William-Dorsch/Open-Source-Train-Controller/train controller parts/automaticBrakeMagnetBase.stl

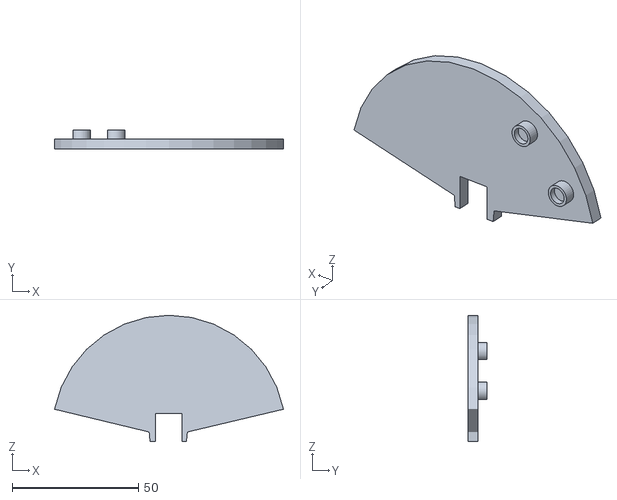
[picture p15: CAD file, 2024-12-01]
train controller parts/automaticBrakeMagnetBase.stl
90.9 x 7.53 x 50.2
