William-Dorsch/Open-Source-Train-Controller/train controller parts/frontWall.stl

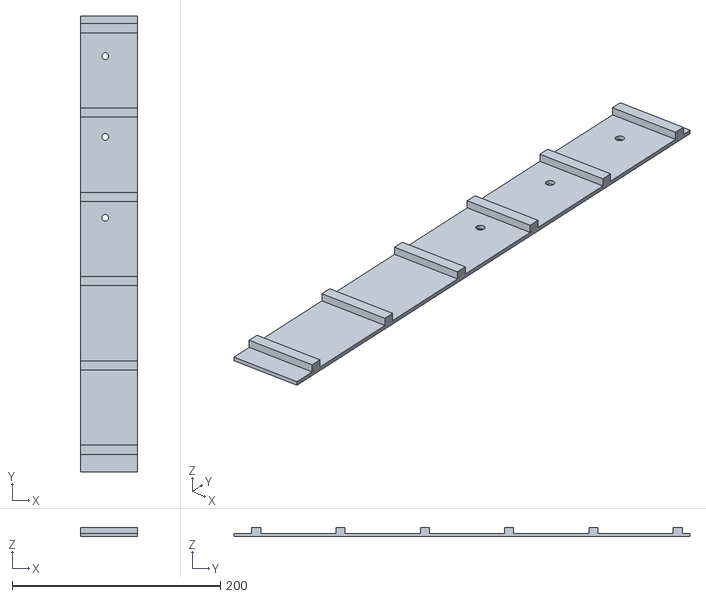
[picture p16: CAD file, 2024-12-01]
train controller parts/frontWall.stl
54.9 x 438.3 x 8.45
