William-Dorsch/Open-Source-Train-Controller/train controller parts/leverWheelBase.stl

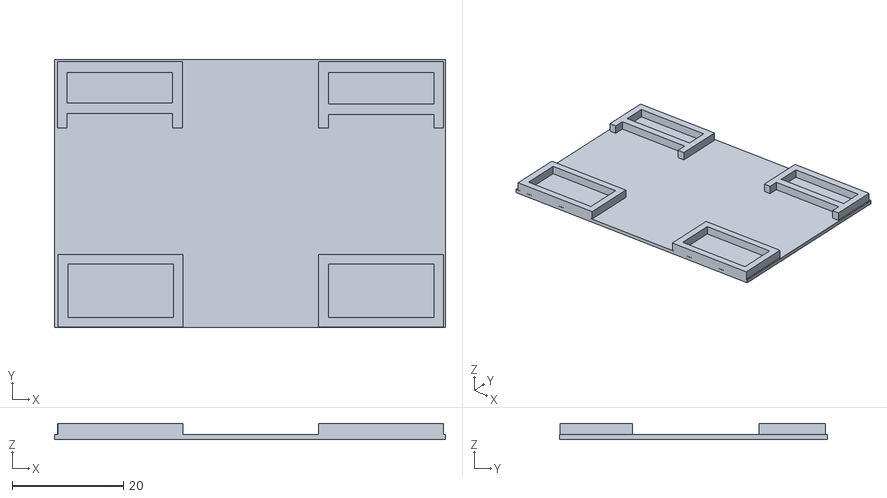
[picture p17: CAD file, 2024-12-01]
train controller parts/leverWheelBase.stl
70.3 x 48.2 x 2.90
