William-Dorsch/Open-Source-Train-Controller/train controller parts/sideWall.stl

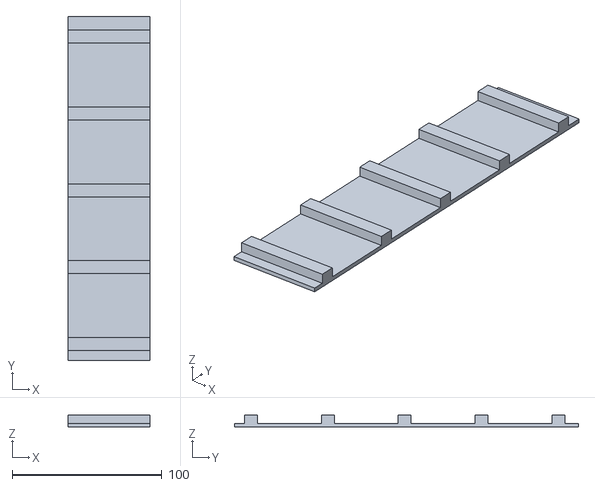
[picture p18: CAD file, 2024-12-01]
train controller parts/sideWall.stl
54.9 x 230.0 x 7.86
