William-Dorsch/Open-Source-Train-Controller/train controller parts/handleBaseRod.stl

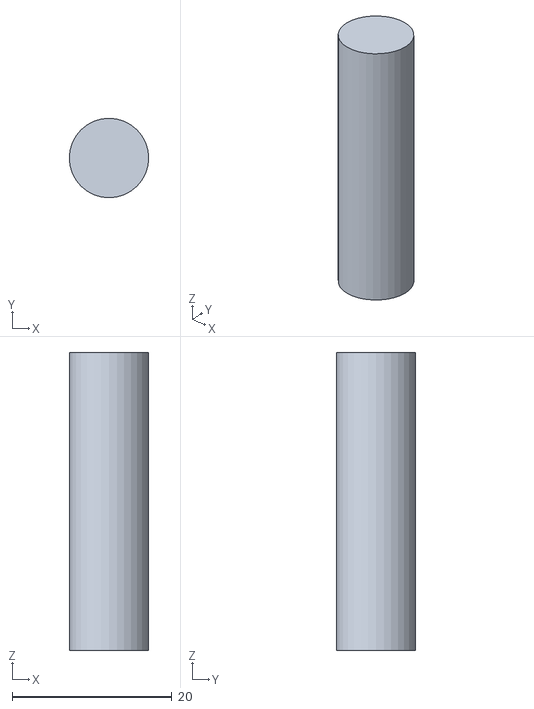
[picture p19: CAD file, 2024-12-01]
train controller parts/handleBaseRod.stl
9.95 x 9.95 x 37.3
