William-Dorsch/Open-Source-Train-Controller/train controller parts/buttonBoardSupports.stl

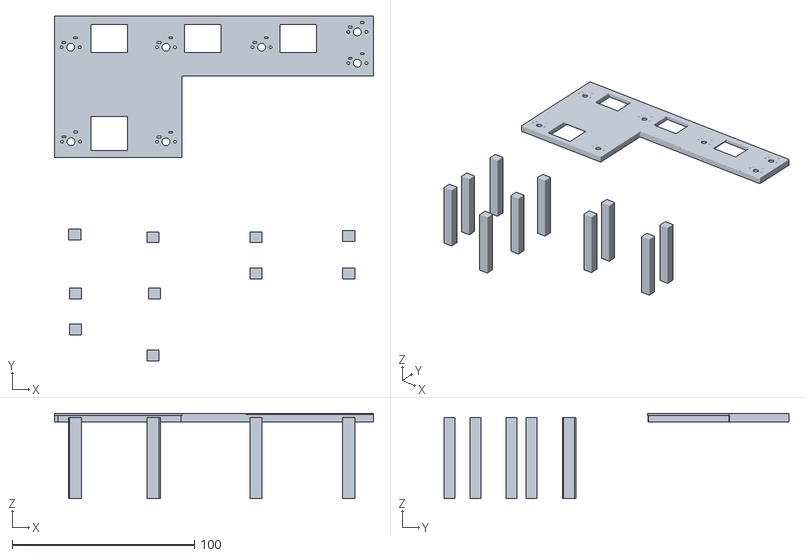
[picture p20: CAD file, 2024-12-01]
train controller parts/buttonBoardSupports.stl
175.0 x 189.2 x 46.6
