William-Dorsch/Open-Source-Train-Controller/train controller parts/lightDial.stl

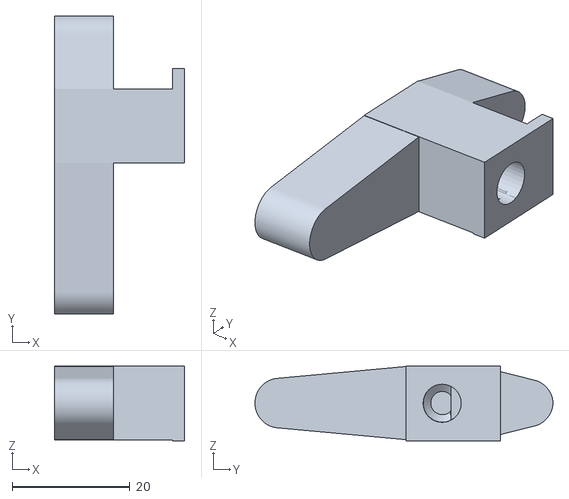
[picture p21: CAD file, 2024-12-01]
train controller parts/lightDial.stl
22.1 x 50.5 x 12.7
