William-Dorsch/Open-Source-Train-Controller/train controller parts/automaticBrakeHandle.stl

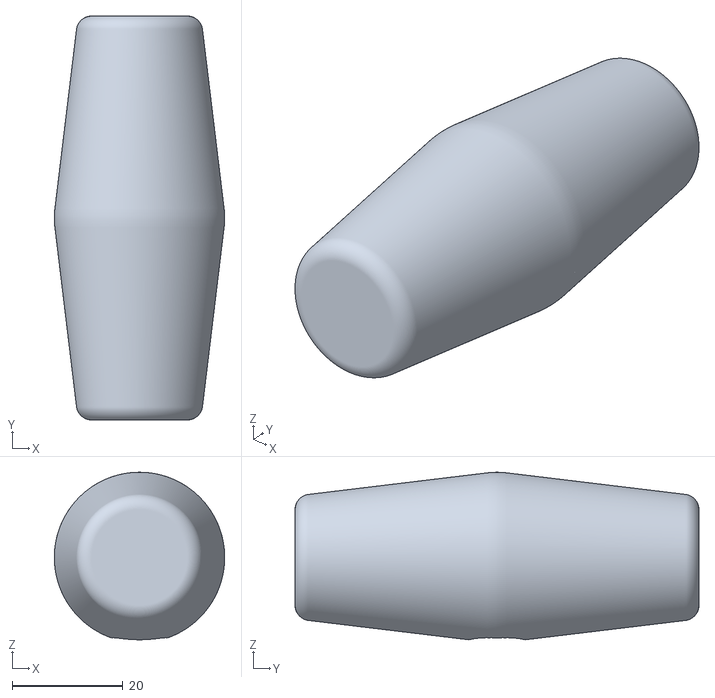
[picture p22: CAD file, 2024-12-01]
train controller parts/automaticBrakeHandle.stl
30.8 x 73.0 x 30.3
