William-Dorsch/Open-Source-Train-Controller/train controller parts/leftLeverCover.stl

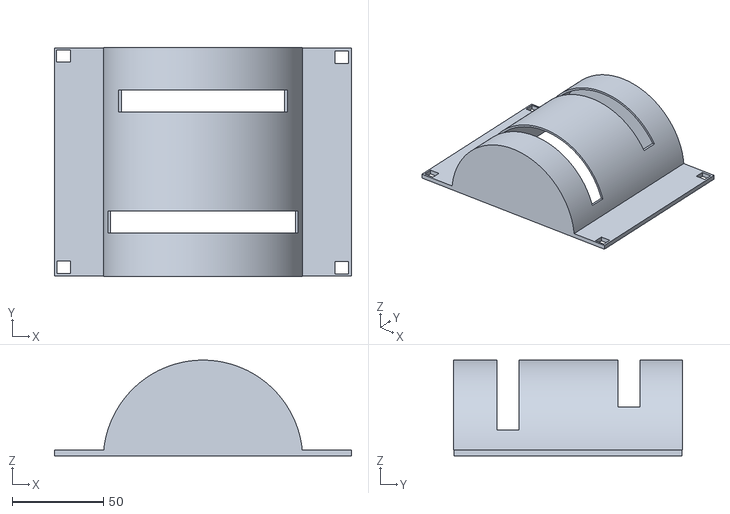
[picture p23: CAD file, 2024-12-01]
train controller parts/leftLeverCover.stl
162.9 x 125.5 x 52.5
