William-Dorsch/Open-Source-Train-Controller/train controller parts/reverserMagnetBase.stl

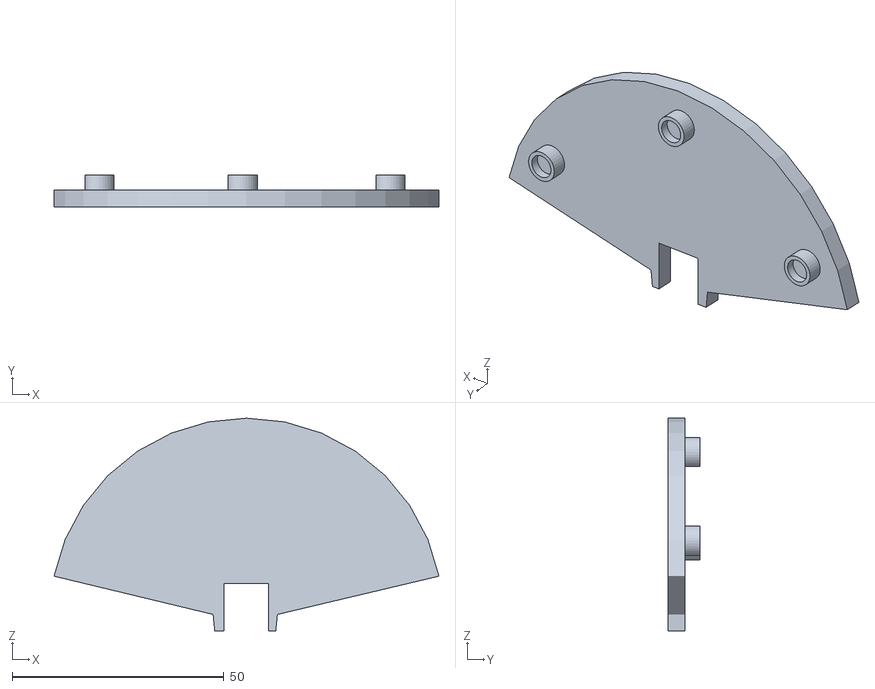
[picture p24: CAD file, 2024-12-01]
train controller parts/reverserMagnetBase.stl
90.9 x 7.53 x 50.2
